go4retro/HalfMegCoCo/pcb/copyright.bmp

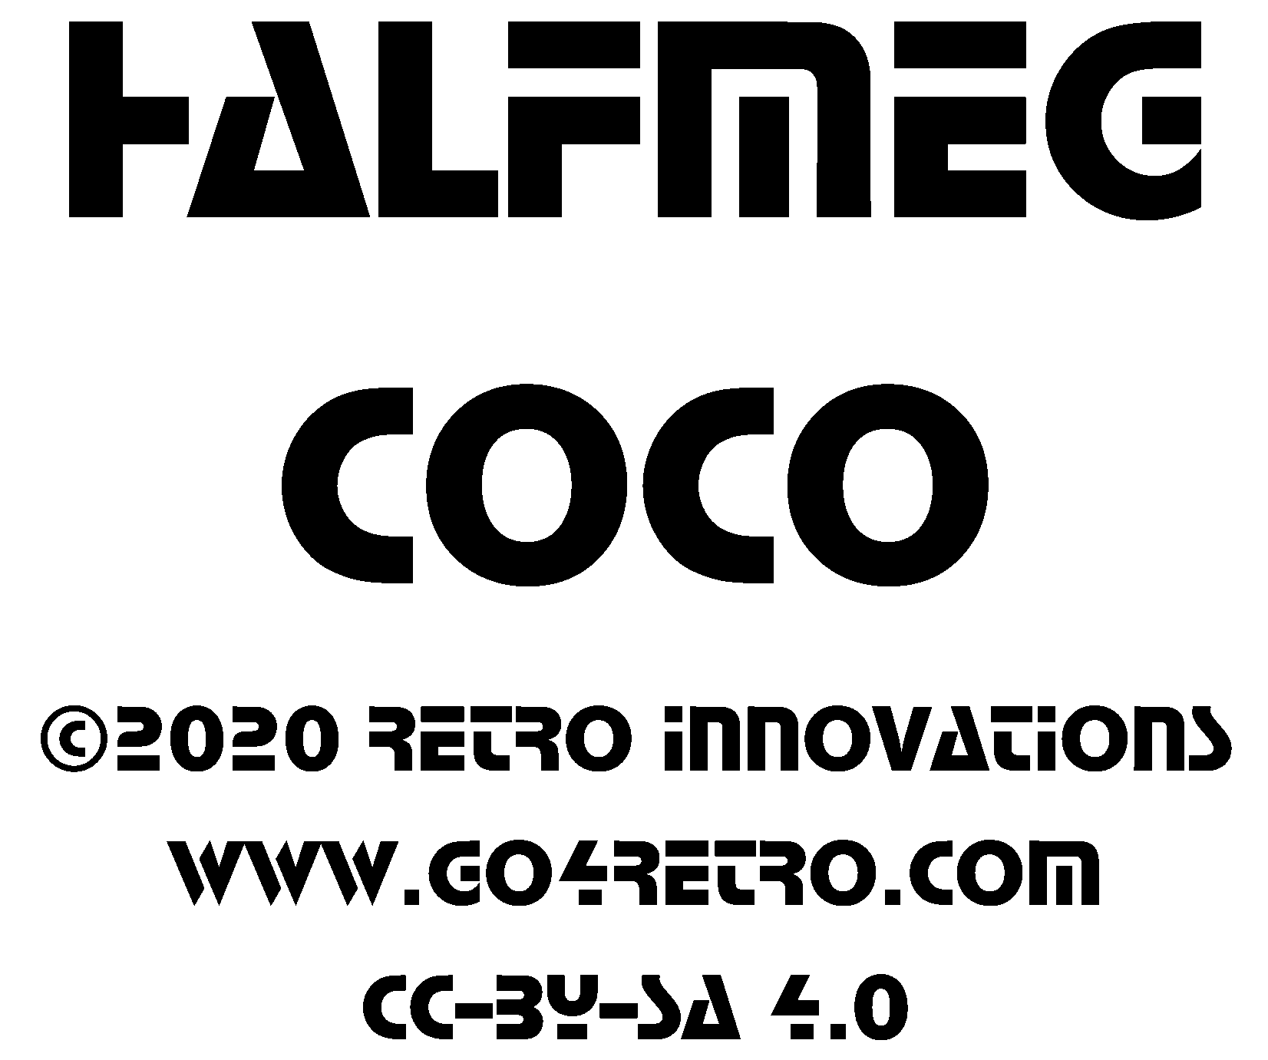
pcb/copyright.bmp
